Kirandawadi/Braille-Embosser/rotary_encoder_test/rotary_encoder_test/braille_codes.h

/*
 * braille.h
 *
 * Created: 6/3/2018 2:12:27 PM
 *  Author: Kiran Dawadi
 */ 


#ifndef BRAILLE_CODES_H_
#define BRAILLE_CODES_H_

#define TRUE 1
extern double linear_position;
extern volatile int  punch_pin[6];


void set_punch_values(char x)
{
	switch('x')
	{
		case 'a':
			punch_pin[0] = 0;
			punch_pin[1] = 0;
			punch_pin[2] = 1;
			punch_pin[3] = 0;
			punch_pin[4] = 0; 
			punch_pin[5] = 0; 
							break;
		
			
		case 'b':
				punch_pin[0] = 0;
				punch_pin[1] = 1;
				punch_pin[2] = 1;
				punch_pin[3] = 0;
				punch_pin[4] = 0;
				punch_pin[5] = 0;
								break;
		
		case 'c':
				punch_pin[0] = 0;
				punch_pin[1] = 0;
				punch_pin[2] = 1;
				punch_pin[3] = 0;
				punch_pin[4] = 0;
				punch_pin[5] = 1;
								break;
		
		case 'd':
		punch_pin[0] = 0;
		punch_pin[1] = 0;
		punch_pin[2] = 1;
		punch_pin[3] = 0;
		punch_pin[4] = 1;
		punch_pin[5] = 1;
		break;
		
		case 'e':
		punch_pin[0] = 0;
		punch_pin[1] = 0;
		punch_pin[2] = 1;
		punch_pin[3] = 0;
		punch_pin[4] = 1;
		punch_pin[5] = 0;
		break;
		
		case 'f':
		punch_pin[0] = 0;
		punch_pin[1] = 1;
		punch_pin[2] = 1;
		punch_pin[3] = 0;
		punch_pin[4] = 0;
		punch_pin[5] = 1;
		break;
		
		case 'g':
		punch_pin[0] = 0;
		punch_pin[1] = 1;
		punch_pin[2] = 1;
		punch_pin[3] = 0;
		punch_pin[4] = 1;
		punch_pin[5] = 1;
		break;
		
		case 'h':
		punch_pin[0] = 0;
		punch_pin[1] = 1;
		punch_pin[2] = 1;
		punch_pin[3] = 0;
		punch_pin[4] = 1;
		punch_pin[5] = 0;
		break;
		
		case 'i':
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
{
	for(int i=0;i<50;i++)
	{
		punch();
		linear_position = linear_position + 0.3;
		set_position_cm(linear_position);
		_delay_ms(500);
		
	}
}

void vertical_dots(void)
{
	for(int i=0;i<50;i++)
	{
		punch();
		paper_slide_forward();
		_delay_ms(500);
		
	}
}


#endif /* BRAILLE_H_ */
